josalcedog-cpu/FIBA/Case/case.jpeg

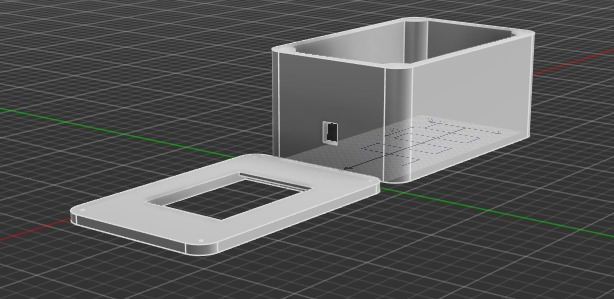
Case/case.jpeg
