josalcedog-cpu/FIBA/Case/case_vista_superior.jpeg

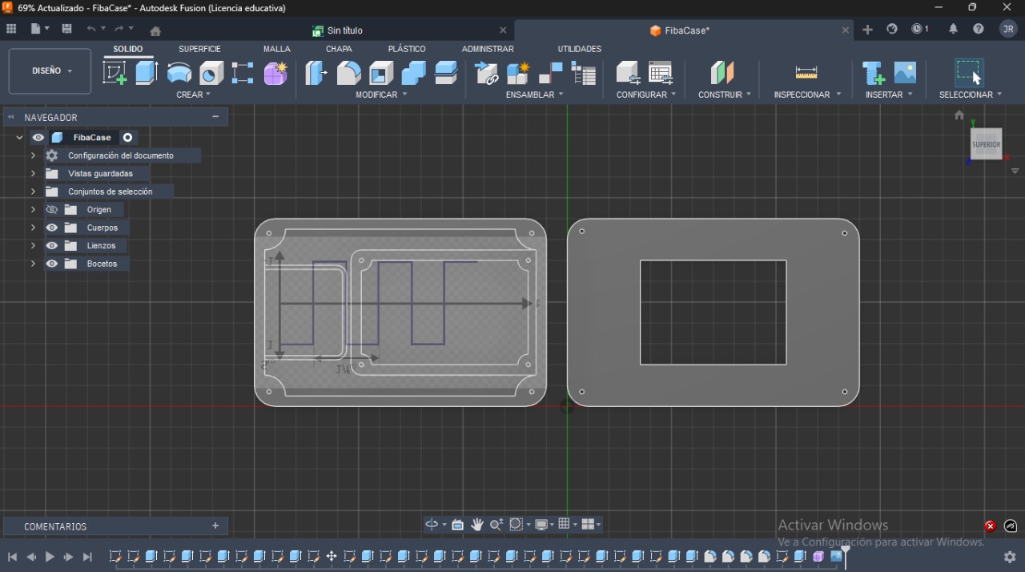
Case/case_vista_superior.jpeg
