josalcedog-cpu/FIBA/Case/Implementacion.jpeg

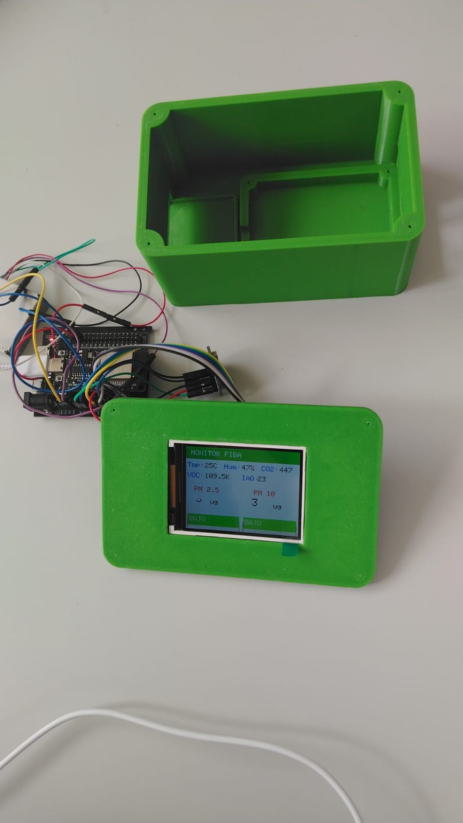
Case/Implementacion.jpeg
