josalcedog-cpu/FIBA/Cronograma.png

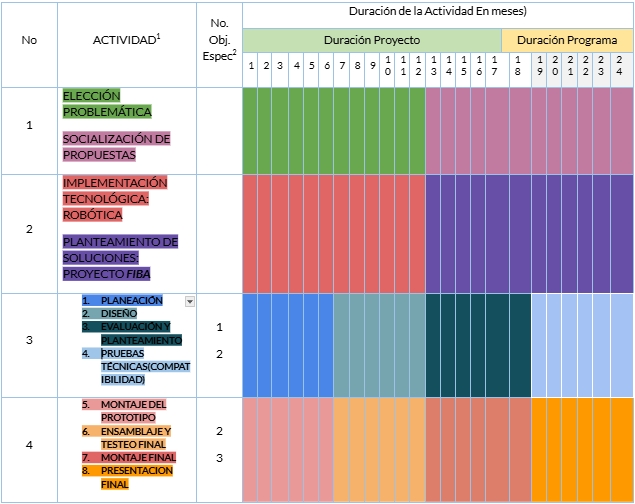
Cronograma.png
