josalcedog-cpu/FIBA/Diagrama_de_caja_negra.jpeg

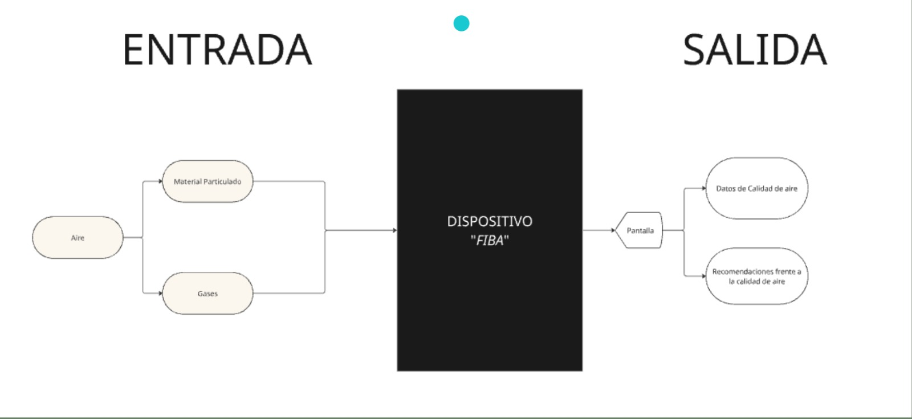
Diagrama_de_caja_negra.jpeg
