josalcedog-cpu/FIBA/Diagrama_general_proyecto.jpeg

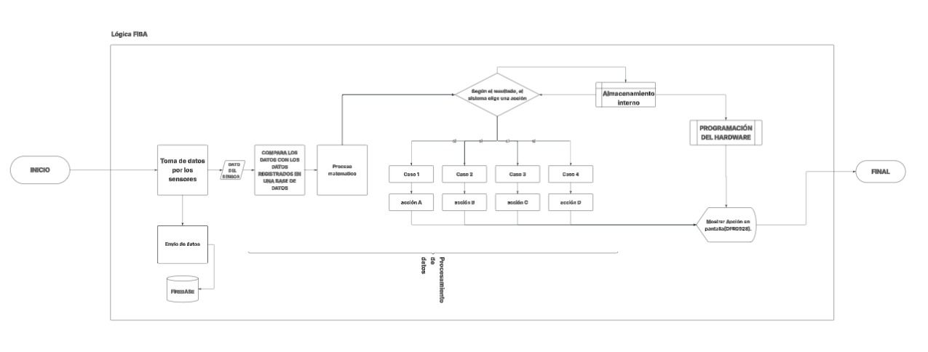
Diagrama_general_proyecto.jpeg
