josalcedog-cpu/FIBA/Diagrama_tecnologico.jpeg

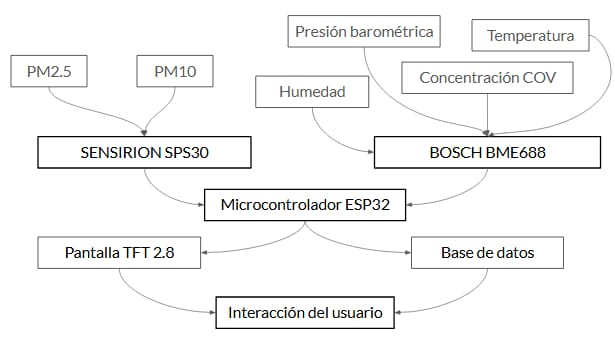
Diagrama_tecnologico.jpeg
