josalcedog-cpu/FIBA/KiCad/impresion_laser.jpeg

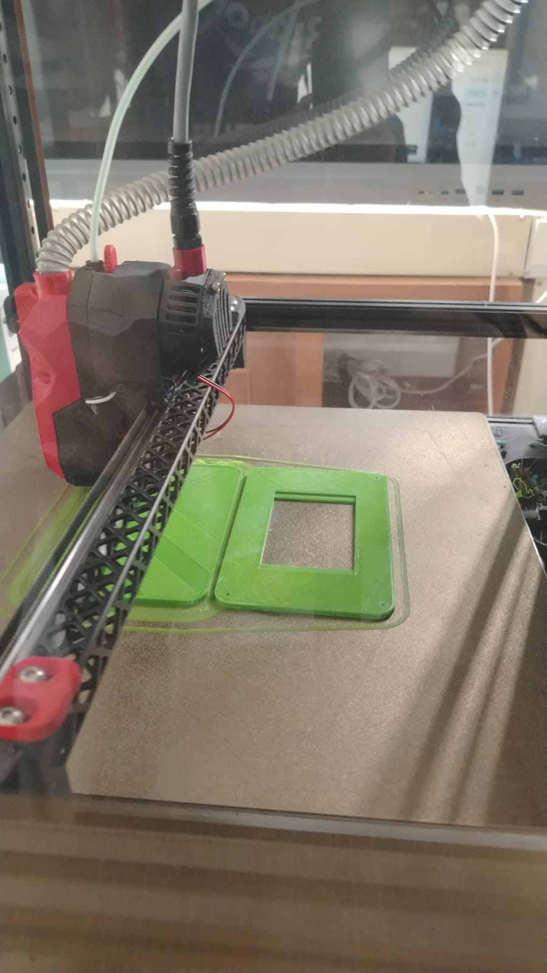
KiCad/impresion_laser.jpeg
