josalcedog-cpu/FIBA/KiCad/layout.png

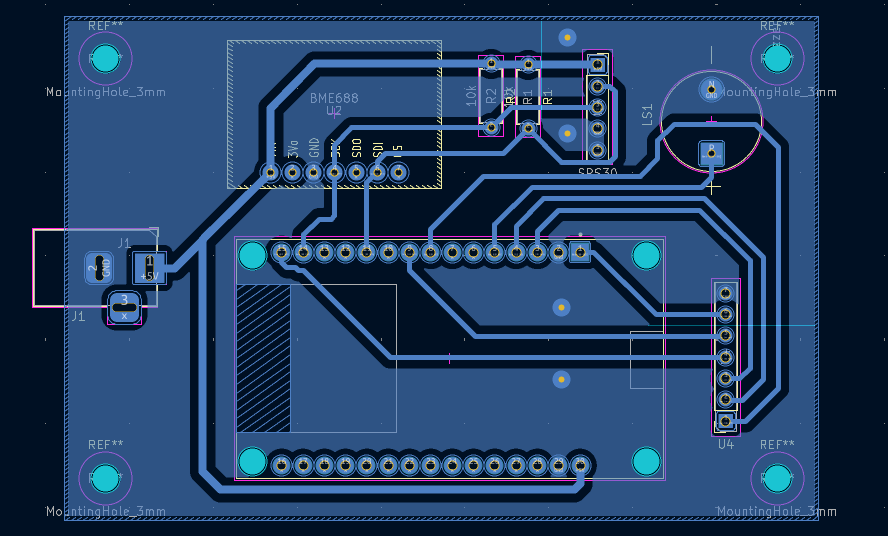
KiCad/layout.png
