josalcedog-cpu/FIBA/KiCad/PCB_frotal.jpeg

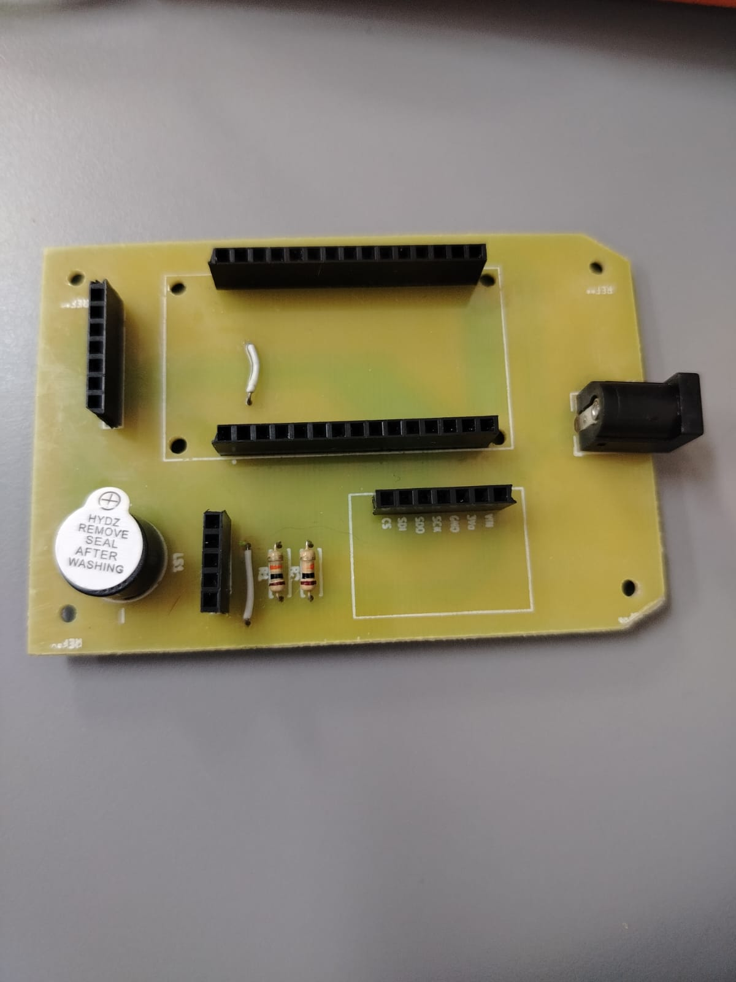
KiCad/PCB_frotal.jpeg
