josalcedog-cpu/FIBA/KiCad/ruteo soldado.jpeg

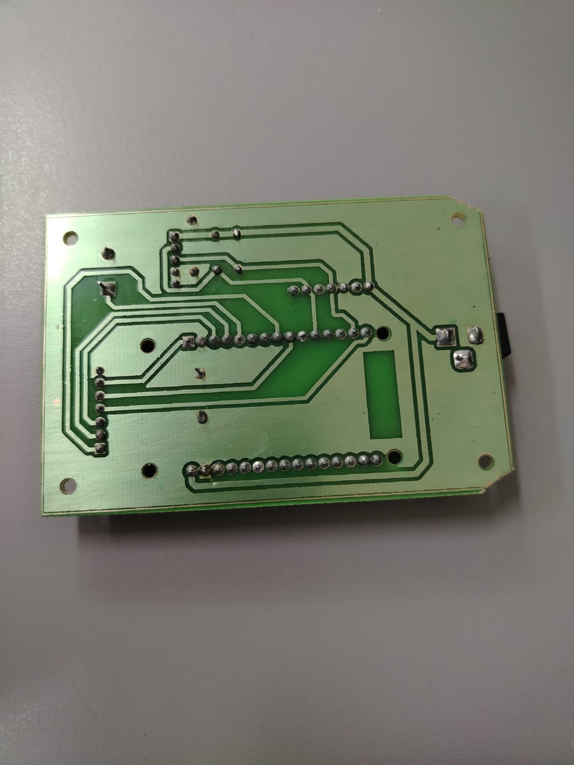
KiCad/ruteo soldado.jpeg
