josalcedog-cpu/FIBA/PCB_case.jpeg

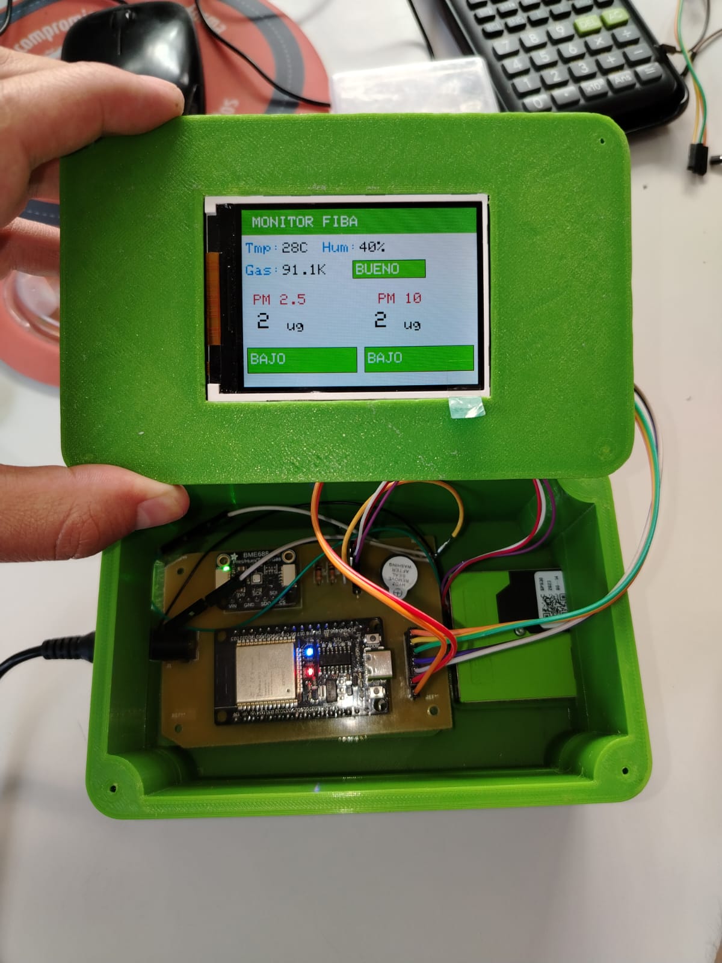
PCB_case.jpeg
