josalcedog-cpu/FIBA/PCB_elementos_soldados.jpeg

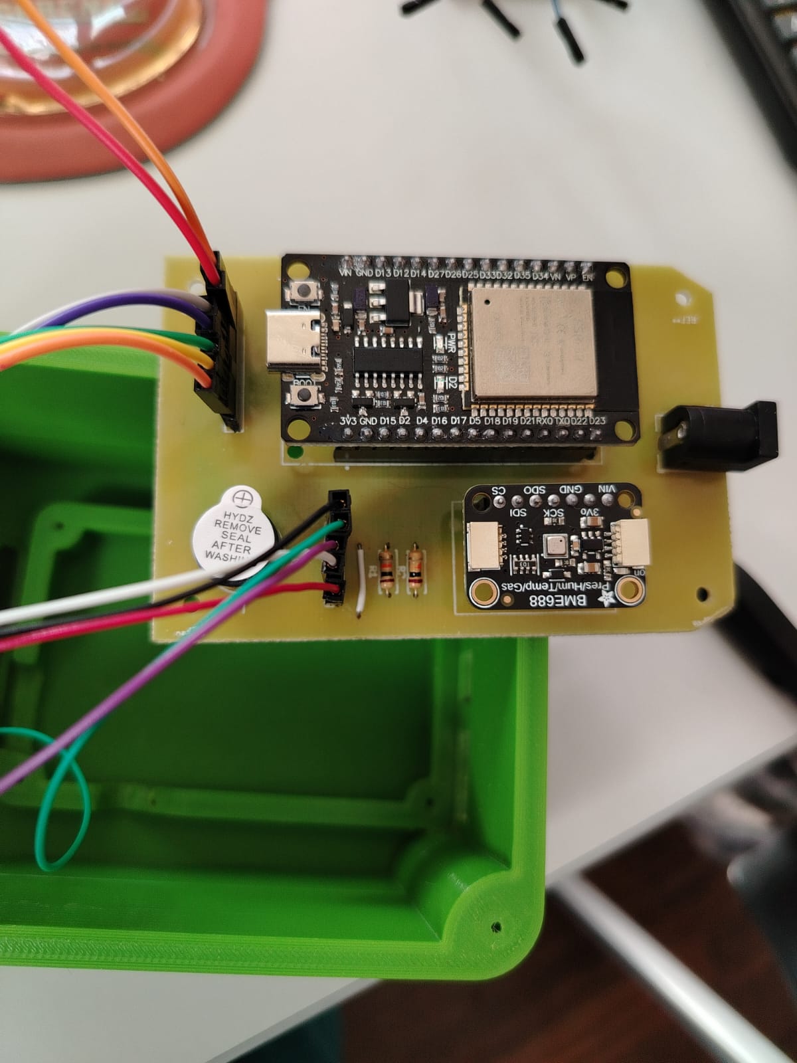
PCB_elementos_soldados.jpeg
