josalcedog-cpu/FIBA/Pruebas Unitarias/TFT28/TFT28.ino

#include <SPI.h>
#include <Adafruit_GFX.h>
#include <Adafruit_ILI9341.h>

#define TFT_CS  5
#define TFT_DC  2
#define TFT_RST 4

Adafruit_ILI9341 tft = Adafruit_ILI9341(TFT_CS, TFT_DC, TFT_RST);


void setup() {
  Serial.begin(115200);
  tft.begin();
  tft.setRotation(1);
  tft.fillScreen(ILI9341_BLACK);

  tft.setTextWrap(true);
  tft.setTextSize(2);
  tft.setTextColor(ILI9341_WHITE);
  tft.setCursor(40, 290);
  tft.print("Hasta luego");

}

void loop() {
  // put your main code here, to run repeatedly:

}
